ChrisChrisLoLo/chaskets1/images/PXL_20230910_224018583.jpg

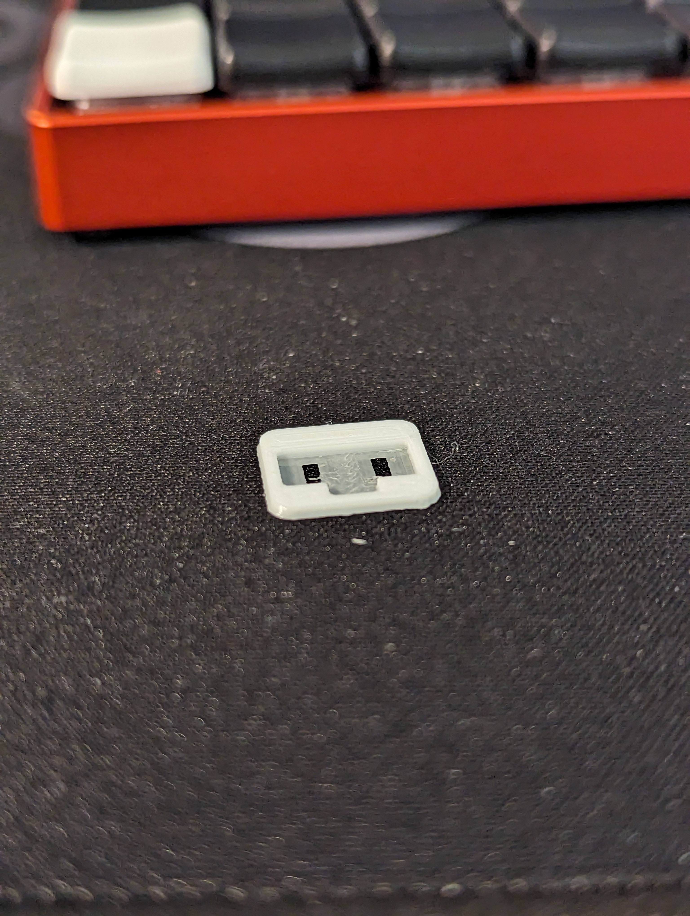
images/PXL_20230910_224018583.jpg
