ChrisChrisLoLo/chaskets1/images/PXL_20230910_224527742.jpg

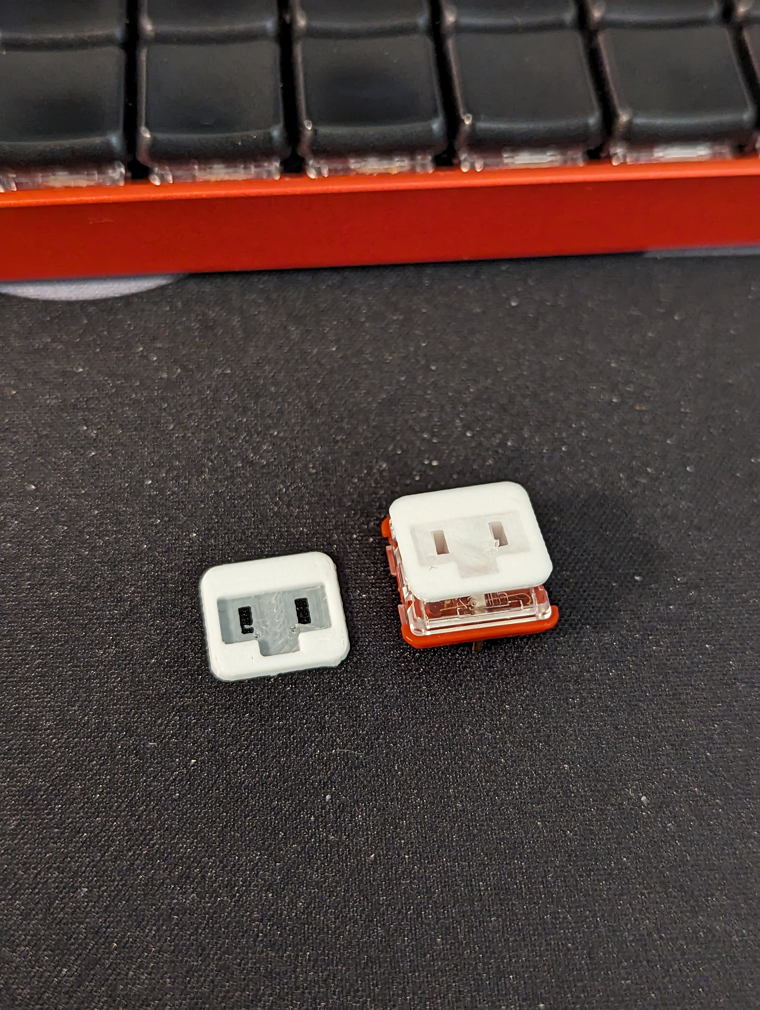
images/PXL_20230910_224527742.jpg
